Ahmed-H300/Pipelined-Processor/schematics/processorDesign/processorDesign.kicad_pcb

## KiCad design 1.Hardware/Daplink_CH552P/Daplink_CH552P.kicad_pcb

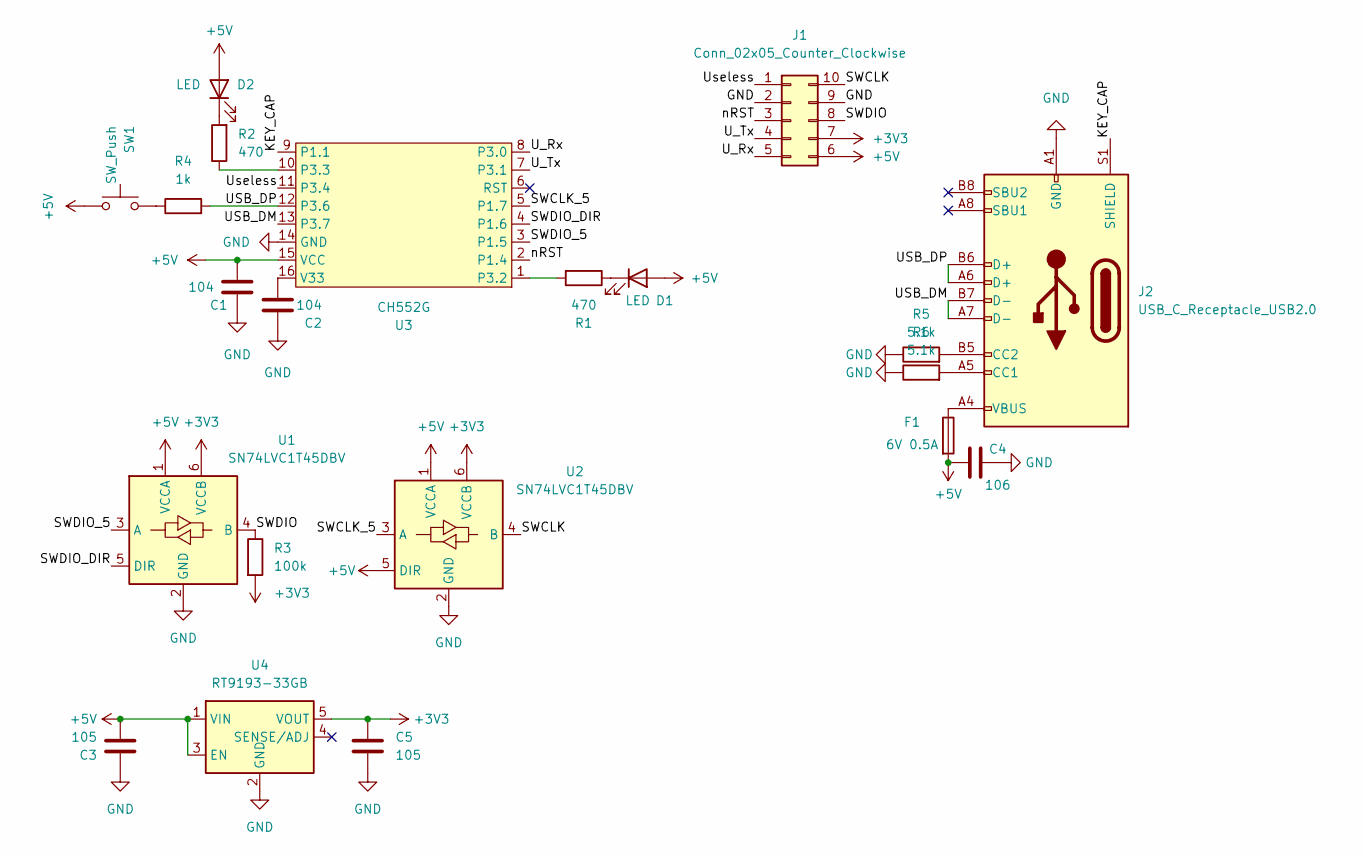
[picture p10: schematic Daplink_CH552P.kicad_sch, Daplink_CH552]

Parts:
C1, C2: 104; C_0603_1608Metric
C3, C5: 105; C_0603_1608Metric
C4: 106; C_0805_2012Metric
D1, D2: LED; LED_0603_1608Metric
F1: 6V 0.5A; Fuse_0603_1608Metric
J1: Conn_02x05_Counter_Clockwise; Connector_2.54mm_2_5P_SMD
J2: USB_C_Receptacle_USB2.0; USB_C_Receptacle_HRO_TYPE-C-31-M-12
R1, R2: 470; R_0603_1608Metric
R3: 100k; R_0603_1608Metric
R4: 1k; R_0603_1608Metric
R5, R6: 5.1k; R_0603_1608Metric
SW1: SW_Push; SW_SPST_B3U-1000P
U1, U2: SN74LVC1T45DBV; SOT-23-6
U3: CH552G; SOP-16_3.9x9.9mm_P1.27mm
U4: RT9193-33GB; TSOT-23-5

Connections:
+3V3: C5.2, J1.7, R3.2, U1.6 (VCCB), U2.6 (VCCB), U4.5 (VOUT)
+5V: C1.1, C3.1, C4.1, D1.2 (A), D2.2 (A), F1.2, J1.6, SW1.1, U1.1 (VCCA), U2.1 (VCCA), U2.5 (DIR), U3.15 (VCC), U4.1 (VIN), U4.3 (EN)
/KEY_CAP: J2.S1 (SHIELD), U3.9 (P1.1)
/SWCLK: J1.10, U2.4 (B)
/SWCLK_5: U2.3 (A), U3.5 (P1.7)
/SWDIO: J1.8, R3.1, U1.4 (B)
/SWDIO_5: U1.3 (A), U3.3 (P1.5)
/SWDIO_DIR: U1.5 (DIR), U3.4 (P1.6)
/USB_DM: J2.A7 (D-), J2.B7 (D-), U3.13 (P3.7)
/USB_DP: J2.A6 (D+), J2.B6 (D+), R4.2, U3.12 (P3.6)
/U_Rx: J1.5, U3.8 (P3.0)
/U_Tx: J1.4, U3.7 (P3.1)
/Useless: J1.1, U3.11 (P3.4)
/nRST: J1.3, U3.2 (P1.4)
GND: C1.2, C2.1, C3.2, C4.2, C5.1, J1.2, J1.9, J2.A1 (GND), J2.A12 (GND), J2.B1 (GND), J2.B12 (GND), R5.1, R6.1, U1.2 (GND), U2.2 (GND), U3.14 (GND), U4.2 (GND)
unnamed: C2.2, U3.16 (V33)
unnamed: D1.1 (K), R1.1
unnamed: D2.1 (K), R2.2
unnamed: F1.1, J2.A4 (VBUS), J2.A9 (VBUS), J2.B4 (VBUS), J2.B9 (VBUS)
unnamed: J2.A5 (CC1), R6.2
unnamed: J2.B5 (CC2), R5.2
unnamed: R1.2, U3.1 (P3.2)
unnamed: R2.1, U3.10 (P3.3)
unnamed: R4.1, SW1.2

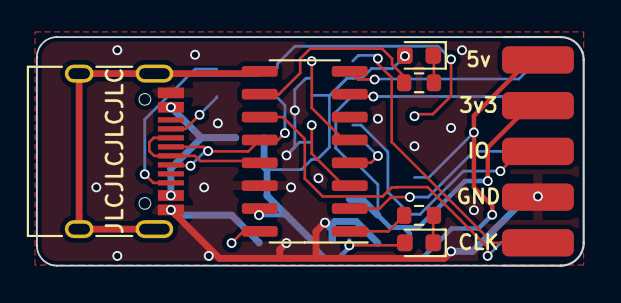
[picture p11: board Daplink_CH552P.kicad_pcb from above]

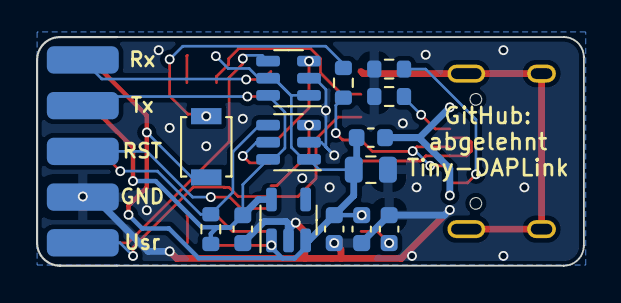
[picture p12: board Daplink_CH552P.kicad_pcb from below]

Board: 2 copper layers, 30.4 x 12.7 mm, 21 parts (15 on the bottom side), 24 nets.
