Ahmed-H300/Pipelined-Processor/codes/verilog files/processor.v

`include "stages/ID.v"
`include "stages/EX.v"	
`include "stages/IF.v"
`include "stages/MEM.v"
`include "stages/WB.v"

`include "intermediate_buffers/EX_MEM.v"
`include "intermediate_buffers/ID_EX.v"
`include "intermediate_buffers/IF_ID.v"
`include "intermediate_buffers/MEM_WB.v"

`include "units/EDU.v"
`include "units/FU1.v"
`include "units/FU2.v"
`include "units/HDU.v"


/*this is our top module which is our processor*/
module processor(EPC, CAUSE, interrupt, reset_in, clk);

/*this is exception program counter that will hold the address of the malfunction instruction*/
output wire [31:0] EPC;

/*this is the reason of exception register that will give exception number pointing out the reason of exception*/
output wire [2:0] CAUSE;

/*this is the reset singal which zeros all the resets except for PC and SP that will hold special value*/
input wire reset_in;

/*this is the clk that's taken as input to the processor and that's really what makes the processor run*/
input wire clk;

/*this is the interrupt signal that's taken as input to the processor and it makes the prcoessor goes into interrupt handler routine*/
input wire interrupt;

/*this is the actual reset signal to the system*/
wire rst_ID;
wire reset;
assign reset = rst_ID | reset_in;

/**************************************************************
	intermediate wires for the IF stage
**************************************************************/

/*outputs*/
wire [31:0] PC_IF;
wire [15:0] instruction_IF;
wire [15:0] Data_IF;
wire INT_IF;


/**************************************************************
	intermediate wires for the IF_ID buffer
	(inputs are the outputs of IF stage)
**************************************************************/

/*outputs*/
wire [31:0] PC_IF_ID_buff;
wire [15:0] instr_IF_ID_buff;
wire [15:0] data_IF_ID_buff;
wire INT_IF_ID_buff;


/**************************************************************
	intermediate wires for the ID stage 
	(inputs comes from an (IF and WB) stages)
**************************************************************/

/*outputs*/
wire [31:0] PC_ID;
wire [3:0] Shmt_ID;
wire [3:0] hash_imm_ID;
wire [15:0] Data_ID;
wire [2:0] Rdst1_ID;
wire [2:0] Rdst2_ID;
wire [3:0] PORT_ID;
wire [2:0] Rsrc_ID;
wire INT_ID;

wire [15:0] Rdst_val_ID;
wire [15:0] Rsrc_val_ID;

wire [1:0] ALU_src1_ID;
wire mem_write_ID;
wire mem_read_ID;
wire reglow_write_ID;
wire reghigh_write_ID;
wire [3:0] ALU_OP_ID;
wire port_write_ID;
wire port_read_ID;
wire mem_type_ID;
wire memToReg_ID;
wire set_Z_ID;
wire set_N_ID;
wire set_C_ID;
wire set_OVF_ID;
wire clr_Z_ID;
wire clr_N_ID;
wire clr_C_ID;
wire clr_OVF_ID;
wire [1:0] jmp_sel_ID;
wire [1:0] SP_src_ID;
wire is_jmp_ID;
wire jmp_src_ID;
wire mem_data_src_ID;
wire mem_addr_src_ID;
wire PC_push_pop_ID;
wire flags_push_pop_ID;

wire set_INT_ID;

/**************************************************************
	intermediate wires for the ID_EX buffer 
	(inputs are ID stage outputs)
**************************************************************/

/*outputs*/
wire [31:0] PC_ID_EX_buff;
wire [3:0] Shmt_ID_EX_buff;
wire [3:0] hash_imm_ID_EX_buff;
wire [15:0] Data_ID_EX_buff;
wire [2:0] Rdst1_ID_EX_buff;
wire [2:0] Rdst2_ID_EX_buff;
wire [3:0] PORT_ID_EX_buff;
wire [2:0] Rsrc_ID_EX_buff;
wire INT_ID_EX_buff;

wire [15:0] Rdst_val_ID_EX_buff;
wire [15:0] Rsrc_val_ID_EX_buff;

wire [1:0] ALU_src1_ID_EX_buff;
wire mem_write_ID_EX_buff;
wire mem_read_ID_EX_buff;
wire reglow_write_ID_EX_buff;
wire reghigh_write_ID_EX_buff;
wire [3:0] ALU_OP_ID_EX_buff;
wire port_write_ID_EX_buff;
wire port_read_ID_EX_buff;
wire mem_type_ID_EX_buff;
wire memToReg_ID_EX_buff;
wire set_Z_ID_EX_buff;
wire set_N_ID_EX_buff;
wire set_C_ID_EX_buff;
wire set_OVF_ID_EX_buff;
wire clr_Z_ID_EX_buff;
wire clr_N_ID_EX_buff;
wire clr_C_ID_EX_buff;
wire clr_OVF_ID_EX_buff;
wire [1:0] jmp_sel_ID_EX_buff;
wire [1:0] SP_src_ID_EX_buff;
wire is_jmp_ID_EX_buff;
wire jmp_src_ID_EX_buff;
wire mem_data_src_ID_EX_buff;
wire mem_addr_src_ID_EX_buff;
wire PC_push_pop_ID_EX_buff;
wire flags_push_pop_ID_EX_buff;


/**************************************************************
	intermediate wires for the EX stage 
	(inputs are coming from ID stage)
**************************************************************/

/*outputs*/
wire [31:0] jmp_addr_EX;
wire do_jmp_EX;
wire [15:0] Rdst1_val_EX;
wire [15:0] Rdst2_val_EX;

wire [31:0] PC_EX;
wire [1:0] SP_src_EX;
wire port_write_EX;
wire port_read_EX;
wire [2:0] Rdst1_EX;
wire mem_write_EX; 
wire mem_read_EX;
wire reglow_write_EX;
wire reghigh_write_EX;
wire [2:0] Rdst2_EX;
wire mem_type_EX;
wire memToReg_EX;
wire [3:0] PORT_EX;
wire [2:0] Rsrc_EX;
wire [15:0] Rsrc_val_EX;
wire mem_data_src_EX;
wire mem_addr_src_EX;
wire [15:0] Rdst_val_EX;
wire INT_EX;
wire PC_push_pop_EX;
wire flags_push_pop_EX;
wire [15:0] ALU_src_val_EX;

/**************************************************************
	intermediate wires for the EX_MEM buffer
	(inputs are coming from the EX stage)
**************************************************************/

/*outputs*/
wire [15:0] Rdst1_val_EX_MEM_buff;
wire [15:0] Rdst2_val_EX_MEM_buff;
wire [31:0] PC_EX_MEM_buff;
wire [1:0] SP_src_EX_MEM_buff;
wire port_write_EX_MEM_buff;
wire port_read_EX_MEM_buff;
wire [2:0] Rdst1_EX_MEM_buff;
wire mem_write_EX_MEM_buff; 
wire mem_read_EX_MEM_buff;
wire reglow_write_EX_MEM_buff;
wire reghigh_write_EX_MEM_buff;
wire [2:0] Rdst2_EX_MEM_buff;
wire mem_type_EX_MEM_buff;
wire memToReg_EX_MEM_buff;
wire [3:0] PORT_EX_MEM_buff;
wire [2:0] Rsrc_EX_MEM_buff;
wire [15:0] Rsrc_val_EX_MEM_buff;
wire mem_data_src_EX_MEM_buff;
wire mem_addr_src_EX_MEM_buff;
wire [15:0] Rdst_val_EX_MEM_buff;
wire INT_EX_MEM_buff;
wire PC_push_pop_EX_MEM_buff;
wire flags_push_pop_EX_MEM_buff;


/**************************************************************
	intermediate wires for the MEM stage
	(inputs comes from the EX/MEM buffer)
**************************************************************/

/*outputs*/

wire [31:0] POP_PC_addr_MEM;
wire POP_PC_sgn_MEM;
wire [3:0] POP_flags_val_MEM;
wire POP_flags_sgn_MEM;
wire stall_MEM; 

wire [15:0] Rdst2_val_MEM;
wire [2:0] Rdst2_MEM;
wire reghigh_write_MEM;
wire reglow_write_MEM;
wire [2:0] Rdst1_MEM;
wire [15:0] Rdst1_val_MEM;
wire [15:0] Data_MEM;
wire memToReg_MEM;
wire [31:0] SP_val_MEM;

/**************************************************************
	intermediate wires for the MEM_WB buffer
	(inputs comes from the MEM stage)
**************************************************************/

/*outputs*/
wire [15:0] Rdst2_val_MEM_WB_buff;
wire [2:0] Rdst2_MEM_WB_buff;
wire reghigh_write_MEM_WB_buff;
wire reglow_write_MEM_WB_buff;
wire [2:0] Rdst1_MEM_WB_buff;
wire [15:0] Rdst1_val_MEM_WB_buff;
wire [15:0] Data_MEM_WB_buff;
wire memToReg_MEM_WB_buff;

/**************************************************************
	intermediate wires for the WB stage
	(inputs comes from the MEM_WB buffer)
**************************************************************/

/*outputs*/
wire [15:0] Rdst2_val_WB;
wire [2:0] Rdst2_WB;
wire reghigh_write_WB;
wire [15:0] Rdst1_val_WB;
wire [2:0] Rdst1_WB;
wire reglow_write_WB;


/**************************************************************
	intermediate wires for the exception detection unit
	(inputs comes from the decode, execute, memory stages)
**************************************************************/

/*outputs*/
wire exception_EDU;			
wire exception_ID_EDU;
wire exception_EXE_EDU;
wire exception_MEM_EDU;


/**************************************************************
	intermediate wires for the hazard detection unit
	(inputs comes from the decode, execute)
**************************************************************/

/*outputs*/
wire stall_HDU;


/**************************************************************
	intermediate wires for the forwarding unit 1
	(inputs comes from the execute, memory, write-back stages)
**************************************************************/

/*outputs*/
wire [1:0] forward_ALU_dst_FU1;
wire [1:0] forward_ALU_src_FU1;
wire forward_Rdst_num_MEM_to_Rdst_FU1;
wire forward_Rdst_num_WB_to_Rdst_FU1;
wire forward_Rdst_num_MEM_to_Rsrc_FU1;
wire forward_Rdst_num_WB_to_Rsrc_FU1;


/**************************************************************
	intermediate wires for the forwarding unit 2
	(inputs comes from the memory, write-back stages)
**************************************************************/

/*outputs*/
wire forward_Rdst1_to_write_data_FU2;
wire forward_Rdst2_to_write_data_FU2;
wire forward_Rdst1_to_address_FU2;
wire forward_Rdst2_to_address_FU2;

/**************************************************************
	connecting the modules(stages) together
**************************************************************/

/*IF stage*/
IF instr_fetch(.PC_IF_out(PC_IF), .instruction(instruction_IF), .Data(Data_IF), .INT(INT_IF), .clk(clk), .reset(reset), .interrupt(interrupt), .exception(exception_EDU),
				.SET_INT(set_INT_ID), .pop_pc(POP_PC_sgn_MEM), .PC_popedValue(POP_PC_addr_MEM), .jmp_sgn(do_jmp_EX), .PC_jmpValue(jmp_addr_EX), .stall(stall_HDU | stall_MEM),
				.PC_IF_ID_in(PC_IF_ID_buff));

/*IF_ID buffer*/
IF_ID fetch_decode_buff(.PC_out(PC_IF_ID_buff), .instruction_out(instr_IF_ID_buff), .Data_out(data_IF_ID_buff), .INT_out(INT_IF_ID_buff), 
						.PC_in(PC_IF), .instruction_in(instruction_IF), .Data_in(Data_IF), .INT_in(INT_IF), .stall(stall_HDU | stall_MEM), .reset(reset | POP_PC_sgn_MEM | do_jmp_EX), 
						.clk(clk), .flush(exception_EDU));
	
/*ID stage*/	
ID instr_decode(.PC_out(PC_ID), .Shmt_out(Shmt_ID), .hash_imm_out(hash_imm_ID), .Data_out(Data_ID), .Rdst1_out(Rdst1_ID), .Rdst_val_out(Rdst_val_ID), .Rsrc_val_out(Rsrc_val_ID),
				.ALU_src1_out(ALU_src1_ID), .mem_write_out(mem_write_ID), .mem_read_out(mem_read_ID), .reglow_write_out(reglow_write_ID), .reghigh_write_out(reghigh_write_ID),
				.ALU_OP_out(ALU_OP_ID), .port_write_out(port_write_ID), .port_read_out(port_read_ID), .Rdst2_out(Rdst2_ID), .mem_type_out(mem_type_ID), .memToReg_out(memToReg_ID),
				.set_Z_out(set_Z_ID), .set_N_out(set_N_ID), .set_C_out(set_C_ID), .set_OVF_out(set_OVF_ID), .clr_Z_out(clr_Z_ID), .clr_N_out(clr_N_ID),.clr_C_out(clr_C_ID), 
				.clr_OVF_out(clr_OVF_ID), .jmp_sel_out(jmp_sel_ID), .SP_src_out(SP_src_ID), .PORT_out(PORT_ID), .Rsrc_out(Rsrc_ID), .is_jmp_out(is_jmp_ID), .jmp_src_out(jmp_src_ID),
				.mem_data_src_out(mem_data_src_ID), .mem_addr_src_out(mem_addr_src_ID), .INT_out(INT_ID), .PC_push_pop_out(PC_push_pop_ID), .flags_push_pop_out(flags_push_pop_ID), .set_INT_out(set_INT_ID),
				.rst_out(rst_ID), .PC_in(PC_IF_ID_buff), .instruction_in(instr_IF_ID_buff), .Data_in(data_IF_ID_buff), .INT_in(INT_IF_ID_buff), .data_to_be_written_low_in(Rdst1_val_WB), 
				.reg_dst_low_in(Rdst1_WB), .reg_write_low_in(reglow_write_WB), .data_to_be_written_high_in(Rdst2_val_WB), .reg_dst_high_in(Rdst2_WB), .reg_write_high_in(reghigh_write_WB), 
				.reset(reset), .clk(clk));

/*ID_EX buffer*/
ID_EX decode_execute_buff(.PC_out(PC_ID_EX_buff), .Shmt_out(Shmt_ID_EX_buff), .hash_imm_out(hash_imm_ID_EX_buff), .Data_out(Data_ID_EX_buff), .Rdst1_out(Rdst1_ID_EX_buff), 
							.Rdst_val_out(Rdst_val_ID_EX_buff), .Rsrc_val_out(Rsrc_val_ID_EX_buff), .ALU_src1_out(ALU_src1_ID_EX_buff), .mem_write_out(mem_write_ID_EX_buff),
							.mem_read_out(mem_read_ID_EX_buff), .reglow_write_out(reglow_write_ID_EX_buff), .reghigh_write_out(reghigh_write_ID_EX_buff), .ALU_OP_out(ALU_OP_ID_EX_buff), 
							.port_write_out(port_write_ID_EX_buff), .port_read_out(port_read_ID_EX_buff), .Rdst2_out(Rdst2_ID_EX_buff), .mem_type_out(mem_type_ID_EX_buff), .memToReg_out(memToReg_ID_EX_buff), 
							.set_Z_out(set_Z_ID_EX_buff), .set_N_out(set_N_ID_EX_buff), .set_C_out(set_C_ID_EX_buff), .set_OVF_out(set_OVF_ID_EX_buff), .clr_Z_out(clr_Z_ID_EX_buff), .clr_N_out(clr_N_ID_EX_buff),
							.clr_C_out(clr_C_ID_EX_buff), .clr_OVF_out(clr_OVF_ID_EX_buff), .jmp_sel_out(jmp_sel_ID_EX_buff), .SP_src_out(SP_src_ID_EX_buff), .PORT_out(PORT_ID_EX_buff), .Rsrc_out(Rsrc_ID_EX_buff), 
							.is_jmp_out(is_jmp_ID_EX_buff), .jmp_src_out(jmp_src_ID_EX_buff), .mem_data_src_out(mem_data_src_ID_EX_buff), .mem_addr_src_out(mem_addr_src_ID_EX_buff), .INT_out(INT_ID_EX_buff), 
							.PC_push_pop_out(PC_push_pop_ID_EX_buff), .flags_push_pop_out(flags_push_pop_ID_EX_buff), .PC_in(PC_ID), .Shmt_in(Shmt_ID), .hash_imm_in(hash_imm_ID), .Data_in(Data_ID), .Rdst1_in(Rdst1_ID), 
							.Rdst_val_in(Rdst_val_ID), .Rsrc_val_in(Rsrc_val_ID), .ALU_src1_in(ALU_src1_ID), .mem_write_in(mem_write_ID), .mem_read_in(mem_read_ID), .reglow_write_in(reglow_write_ID), .reghigh_write_in(reghigh_write_ID),
							.ALU_OP_in(ALU_OP_ID), .port_write_in(port_write_ID), .port_read_in(port_read_ID), .Rdst2_in(Rdst2_ID), .mem_type_in(mem_type_ID), .memToReg_in(memToReg_ID), .set_Z_in(set_Z_ID), .set_N_in(set_N_ID), 
							.set_C_in(set_C_ID), .set_OVF_in(set_OVF_ID), .clr_Z_in(clr_Z_ID), .clr_N_in(clr_N_ID), .clr_C_in(clr_C_ID), .clr_OVF_in(clr_OVF_ID), .jmp_sel_in(jmp_sel_ID), .SP_src_in(SP_src_ID), .PORT_in(PORT_ID),
							.Rsrc_in(Rsrc_ID), .is_jmp_in(is_jmp_ID), .jmp_src_in(jmp_src_ID), .mem_data_src_in(mem_data_src_ID), .mem_addr_src_in(mem_addr_src_ID), .INT_in(INT_ID), .PC_push_pop_in(PC_push_pop_ID),
							.flags_push_pop_in(flags_push_pop_ID), .stall(stall_MEM), .reset(POP_PC_sgn_MEM | reset), .clk(clk), .flush(stall_HDU | exception_EXE_EDU | exception_MEM_EDU));

/*EX stage*/	
EX instr_execute(.PC_out(PC_EX), .SP_src_out(SP_src_EX), .port_write_out(port_write_EX), .port_read_out(port_read_EX), .Rdst1_val_out(Rdst1_val_EX), .Rdst1_out(Rdst1_EX), 
				.mem_write_out(mem_write_EX), .mem_read_out(mem_read_EX), .reglow_write_out(reglow_write_EX), .reghigh_write_out(reghigh_write_EX), .Rdst2_out(Rdst2_EX), 
				.mem_type_out(mem_type_EX), .memToReg_out(memToReg_EX), .Rdst2_val_out(Rdst2_val_EX), .PORT_out(PORT_EX), .Rsrc_out(Rsrc_EX), .Rsrc_val_out(Rsrc_val_EX), 
				.mem_data_src_out(mem_data_src_EX), .mem_addr_src_out(mem_addr_src_EX), .Rdst_val_out(Rdst_val_EX), .INT_out(INT_EX), .PC_push_pop_out(PC_push_pop_EX),
				.flags_push_pop_out(flags_push_pop_EX), .jmp_addr_out(jmp_addr_EX), .do_jmp_out(do_jmp_EX), .ALU_src_val_out(ALU_src_val_EX), .PC_in(PC_ID_EX_buff), .Shmt_in(Shmt_ID_EX_buff), .hash_imm_in(hash_imm_ID_EX_buff), 
				.Data_in(Data_ID_EX_buff), .Rdst1_in(Rdst1_ID_EX_buff), .Rdst_val_in(Rdst_val_ID_EX_buff), .Rsrc_val_in(Rsrc_val_ID_EX_buff), .ALU_src1_in(ALU_src1_ID_EX_buff), 
				.mem_write_in(mem_write_ID_EX_buff), .mem_read_in(mem_read_ID_EX_buff), .reglow_write_in(reglow_write_ID_EX_buff), .reghigh_write_in(reghigh_write_ID_EX_buff), 
				.ALU_OP_in(ALU_OP_ID_EX_buff), .port_write_in(port_write_ID_EX_buff), .port_read_in(port_read_ID_EX_buff), .Rdst2_in(Rdst2_ID_EX_buff), .mem_type_in(mem_type_ID_EX_buff), 
				.memToReg_in(memToReg_ID_EX_buff), .set_Z_in(set_Z_ID_EX_buff), .set_N_in(set_N_ID_EX_buff), .set_C_in(set_C_ID_EX_buff), .set_OVF_in(set_OVF_ID_EX_buff),
				.clr_Z_in(clr_Z_ID_EX_buff), .clr_N_in(clr_N_ID_EX_buff), .clr_C_in(clr_C_ID_EX_buff), .clr_OVF_in(clr_OVF_ID_EX_buff), .jmp_sel_in(jmp_sel_ID_EX_buff), 
				.SP_src_in(SP_src_ID_EX_buff), .PORT_in(PORT_ID_EX_buff), .Rsrc_in(Rsrc_ID_EX_buff), .is_jmp_in(is_jmp_ID_EX_buff), .jmp_src_in(jmp_src_ID_EX_buff), 
				.mem_data_src_in(mem_data_src_ID_EX_buff), .mem_addr_src_in(mem_addr_src_ID_EX_buff), .INT_in(INT_ID_EX_buff), .PC_push_pop_in(PC_push_pop_ID_EX_buff), 
				.flags_push_pop_in(flags_push_pop_ID_EX_buff), .POP_flags_val_in(POP_flags_val_MEM), .is_POP_flags_in(POP_flags_sgn_MEM), . Rdst1_val_MEM_in(Rdst1_val_EX_MEM_buff),
				.Rdst2_val_MEM_in(Rdst2_val_EX_MEM_buff), .Rdst1_DATA_val_WB_in(Rdst1_val_WB), .Rdst2_val_WB_in(Rdst2_val_MEM_WB_buff), .forward_ALU_dst_FU1_in(forward_ALU_dst_FU1),
				.forward_ALU_src_FU1_in(forward_ALU_src_FU1), .forward_Rdst_num_MEM_to_Rdst_FU1_in(forward_Rdst_num_MEM_to_Rdst_FU1), .forward_Rdst_num_WB_to_Rdst_FU1_in(forward_Rdst_num_WB_to_Rdst_FU1), 
				.forward_Rdst_num_MEM_to_Rsrc_FU1_in(forward_Rdst_num_MEM_to_Rsrc_FU1), .forward_Rdst_num_WB_to_Rsrc_FU1_in(forward_Rdst_num_WB_to_Rsrc_FU1), 
				.stall_CCR_POP(mem_read_EX_MEM_buff & (PC_push_pop_EX_MEM_buff | flags_push_pop_EX_MEM_buff)), .clk(clk), .reset(reset));

/*EX_MEM buffer*/
EX_MEM execute_memory_buff(.PC_out(PC_EX_MEM_buff), .SP_src_out(SP_src_EX_MEM_buff), .port_write_out(port_write_EX_MEM_buff), .port_read_out(port_read_EX_MEM_buff), 
							.Rdst1_val_out(Rdst1_val_EX_MEM_buff), .Rdst1_out(Rdst1_EX_MEM_buff), .mem_write_out(mem_write_EX_MEM_buff), .mem_read_out(mem_read_EX_MEM_buff), 
							.reglow_write_out(reglow_write_EX_MEM_buff), .reghigh_write_out(reghigh_write_EX_MEM_buff), .Rdst2_out(Rdst2_EX_MEM_buff), .mem_type_out(mem_type_EX_MEM_buff), 
							.memToReg_out(memToReg_EX_MEM_buff), .Rdst2_val_out(Rdst2_val_EX_MEM_buff), .PORT_out(PORT_EX_MEM_buff), .Rsrc_out(Rsrc_EX_MEM_buff), .Rsrc_val_out(Rsrc_val_EX_MEM_buff), 
							.mem_data_src_out(mem_data_src_EX_MEM_buff), .mem_addr_src_out(mem_addr_src_EX_MEM_buff), .Rdst_val_out(Rdst_val_EX_MEM_buff), .INT_out(INT_EX_MEM_buff), 
							.PC_push_pop_out(PC_push_pop_EX_MEM_buff), .flags_push_pop_out(flags_push_pop_EX_MEM_buff), .PC_in(PC_EX), .SP_src_in(SP_src_EX), .port_write_in(port_write_EX), 
							.port_read_in(port_read_EX), .Rdst1_val_in(Rdst1_val_EX), .Rdst1_in(Rdst1_EX), .mem_write_in(mem_write_EX), .mem_read_in(mem_read_EX), 
							.reglow_write_in(reglow_write_EX), .reghigh_write_in(reghigh_write_EX), .Rdst2_in(Rdst2_EX), .mem_type_in(mem_type_EX), .memToReg_in(memToReg_EX), 
							.Rdst2_val_in(Rdst2_val_EX), .PORT_in(PORT_EX), .Rsrc_in(Rsrc_EX), .Rsrc_val_in(Rsrc_val_EX), .mem_data_src_in(mem_data_src_EX), .mem_addr_src_in(mem_addr_src_EX), 
							.Rdst_val_in(Rdst_val_EX), .INT_in(INT_EX), .PC_push_pop_in(PC_push_pop_EX), .flags_push_pop_in(flags_push_pop_EX), .clk(clk), .reset(reset), .stall(stall_MEM),
							.flush(exception_MEM_EDU));

/*MEM stage*/
MEM instr_memory(.Rdst2_val_out(Rdst2_val_MEM), .Rdst2_out(Rdst2_MEM), .reghigh_write_out(reghigh_write_MEM), .reglow_write_out(reglow_write_MEM), .Rdst1_out(Rdst1_MEM), 
				.Rdst1_val_out(Rdst1_val_MEM), .Data_out(Data_MEM), .memToReg_out(memToReg_MEM), .POP_PC_addr_out(POP_PC_addr_MEM), .POP_PC_sgn_out(POP_PC_sgn_MEM),
				.POP_flags_val_out(POP_flags_val_MEM), .POP_flags_sgn_out(POP_flags_sgn_MEM), .stall_out(stall_MEM), .SP_val_out(SP_val_MEM), .PC_in(PC_EX_MEM_buff), .SP_src_in(SP_src_EX_MEM_buff), 
				.port_write_in(port_write_EX_MEM_buff), .port_read_in(port_read_EX_MEM_buff), .Rdst1_val_in(Rdst1_val_EX_MEM_buff), .Rdst1_in(Rdst1_EX_MEM_buff), 
				.mem_write_in(mem_write_EX_MEM_buff), .mem_read_in(mem_read_EX_MEM_buff), .reglow_write_in(reglow_write_EX_MEM_buff), .reghigh_write_in(reghigh_write_EX_MEM_buff),
				.Rdst2_in(Rdst2_EX_MEM_buff), .mem_type_in(mem_type_EX_MEM_buff), .memToReg_in(memToReg_EX_MEM_buff), .Rdst2_val_in(Rdst2_val_EX_MEM_buff), .PORT_in(PORT_EX_MEM_buff),
				.Rsrc_in(Rsrc_EX_MEM_buff), .Rsrc_val_in(Rsrc_val_EX_MEM_buff), .mem_data_src_in(mem_data_src_EX_MEM_buff), .mem_addr_src_in(mem_addr_src_EX_MEM_buff), 
				.Rdst_val_in(Rdst_val_EX_MEM_buff), .INT_in(INT_EX_MEM_buff), .PC_push_pop_in(PC_push_pop_EX_MEM_buff), .flags_push_pop_in(flags_push_pop_EX_MEM_buff), 
				.DATA_Rdst1_WB_in(Rdst1_val_WB), .Rdst2_WB_in(Rdst2_val_WB), .forward_Rdst1_to_write_data_FU2_in(forward_Rdst1_to_write_data_FU2), 
				.forward_Rdst2_to_write_data_FU2_in(forward_Rdst2_to_write_data_FU2), .forward_Rdst1_to_address_FU2_in(forward_Rdst1_to_address_FU2),
				.forward_Rdst2_to_address_FU2_in(forward_Rdst2_to_address_FU2), .reset(reset), .clk(clk));

/*MEM_WB buffer*/
MEM_WB memory_writeBack_buff(.Rdst2_val_out(Rdst2_val_MEM_WB_buff), .Rdst2_out(Rdst2_MEM_WB_buff), .reghigh_write_out(reghigh_write_MEM_WB_buff), .reglow_write_out(reglow_write_MEM_WB_buff), 
							 .Rdst1_out(Rdst1_MEM_WB_buff), .Rdst1_val_out(Rdst1_val_MEM_WB_buff), .Data_out(Data_MEM_WB_buff), .memToReg_out(memToReg_MEM_WB_buff),
							 .Rdst2_val_in(Rdst2_val_MEM), .Rdst2_in(Rdst2_MEM), .reghigh_write_in(reghigh_write_MEM), .reglow_write_in(reglow_write_MEM), 
							 .Rdst1_in(Rdst1_MEM), .Rdst1_val_in(Rdst1_val_MEM), .Data_in(Data_MEM), .memToReg_in(memToReg_MEM), .stall(1'b0), .reset(reset), .clk(clk),
							 .flush(POP_PC_sgn_MEM));

/*WB stage*/	
WB instr_WB(.Rdst2_val_out(Rdst2_val_WB), .Rdst2_out(Rdst2_WB), .reghigh_write_out(reghigh_write_WB), .reglow_write_out(reglow_write_WB), .Rdst1_out(Rdst1_WB), 
			.Rdst1_val_out(Rdst1_val_WB), .Rdst2_val_in(Rdst2_val_MEM_WB_buff), .Rdst2_in(Rdst2_MEM_WB_buff), .reghigh_write_in(reghigh_write_MEM_WB_buff), 
			.reglow_write_in(reglow_write_MEM_WB_buff), .Rdst1_in(Rdst1_MEM_WB_buff), .Rdst1_val_in(Rdst1_val_MEM_WB_buff), .Data_in(Data_MEM_WB_buff), 
			.memToReg_in(memToReg_MEM_WB_buff));


/**************************************************************
	Additional external units
**************************************************************/

/*exception detection unit*/
EDU exception_unit(	.exception_out(exception_EDU), .exception_ID_out(exception_ID_EDU), .exception_EXE_out(exception_EXE_EDU), .exception_MEM_out(exception_MEM_EDU), 
					.CAUSE_out(CAUSE), .EPC_out(EPC), .instrOpCode_in(instr_IF_ID_buff[15:12]), .Rsrc_val_Mem_in(Rsrc_val_EX_MEM_buff), .mem_write_MEM_in(mem_write_EX_MEM_buff),
					.mem_read_MEM_in(mem_read_EX_MEM_buff), .SP_MEM_in(SP_val_MEM), .is_jmp_EX_in(do_jmp_EX), .jmp_addr_EX_in(jmp_addr_EX), .ALU_OP_in(ALU_OP_ID_EX_buff), 
					.Rsrc_val_EX_in(ALU_src_val_EX), .PC_ID_in(PC_IF_ID_buff), .PC_EXE_in(PC_ID_EX_buff), .PC_MEM_in(PC_EX_MEM_buff), .clk(clk), .reset(reset));
		
/*hazard detection unit*/
HDU hazard_unit(.HDU_stall_out(stall_HDU), .Rdst1_EX_in(Rdst1_ID_EX_buff), .mem_read_EX_in(mem_read_ID_EX_buff), .Rdst_ID_in(instr_IF_ID_buff[11:9]), 
				.Rsrc_ID_in(instr_IF_ID_buff[8:6]), .inst_opcode_ID_in(instr_IF_ID_buff[15:12]));

/*forwarding unit 1 (ALU-ALU or MEM-ALU)*/
FU1 forwarding_unit_1(.forward_ALU_dst_out(forward_ALU_dst_FU1), .forward_ALU_src_out(forward_ALU_src_FU1), .forward_Rdst_num_MEM_to_Rdst_out(forward_Rdst_num_MEM_to_Rdst_FU1), 
						.forward_Rdst_num_WB_to_Rdst_out(forward_Rdst_num_WB_to_Rdst_FU1), .forward_Rdst_num_MEM_to_Rsrc_out(forward_Rdst_num_MEM_to_Rsrc_FU1),
						.forward_Rdst_num_WB_to_Rsrc_out(forward_Rdst_num_WB_to_Rsrc_FU1), .Rdst2_wb_WB_in(reghigh_write_MEM_WB_buff), .Rdst1_wb_WB_in(reglow_write_MEM_WB_buff),
						.Rdst1_WB_in(Rdst1_MEM_WB_buff), .Rdst2_WB_in(Rdst2_MEM_WB_buff), .Rdst1_wb_mem_in(reglow_write_EX_MEM_buff), .Rdst2_wb_mem_in(reghigh_write_EX_MEM_buff), 
						.Rdst1_mem_in(Rdst1_EX_MEM_buff), .Rdst2_mem_in(Rdst2_EX_MEM_buff), .Rsrc_EX_in(Rsrc_ID_EX_buff), .Rdst_EX_in(Rdst1_ID_EX_buff));

/*forwarding unit 2 (MEM-MEM)*/
FU2 forwarding_unit_2(.forward_Rdst1_to_write_data_out(forward_Rdst1_to_write_data_FU2), .forward_Rdst2_to_write_data_out(forward_Rdst2_to_write_data_FU2), 
						.forward_Rdst1_to_address_out(forward_Rdst1_to_address_FU2), .forward_Rdst2_to_address_out(forward_Rdst2_to_address_FU2), .Rdst1_WB_in(Rdst1_MEM_WB_buff),
						.Rdst2_WB_in(Rdst2_MEM_WB_buff), .Rdst_MEM_in(Rdst1_EX_MEM_buff), .Rsrc_MEM_in(Rsrc_EX_MEM_buff), .reg_low_write_WB(reglow_write_WB), 
						.reg_high_write_WB(reghigh_write_WB));

endmodule
